PaulZC/Iridium_9603N_Solar_Beacon/img/Iridium_9603N_Solar_Beacon_4.JPG

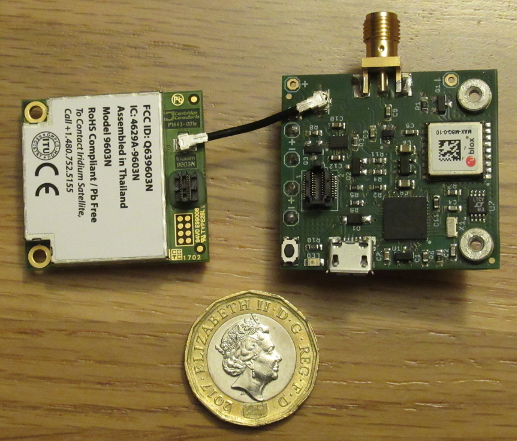
img/Iridium_9603N_Solar_Beacon_4.JPG
