PaulZC/Iridium_9603N_Solar_Beacon/Iridium_9603N_Solar_Beacon_Prototype.JPG

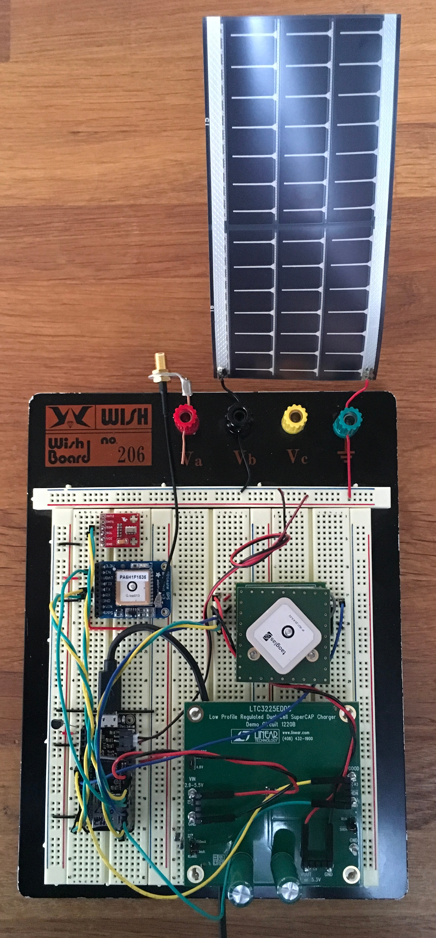
Iridium_9603N_Solar_Beacon_Prototype.JPG
