PaulZC/Iridium_9603N_Solar_Beacon/Iridium_9603N_Solar_Beacon_Prototype_Fritzing.png

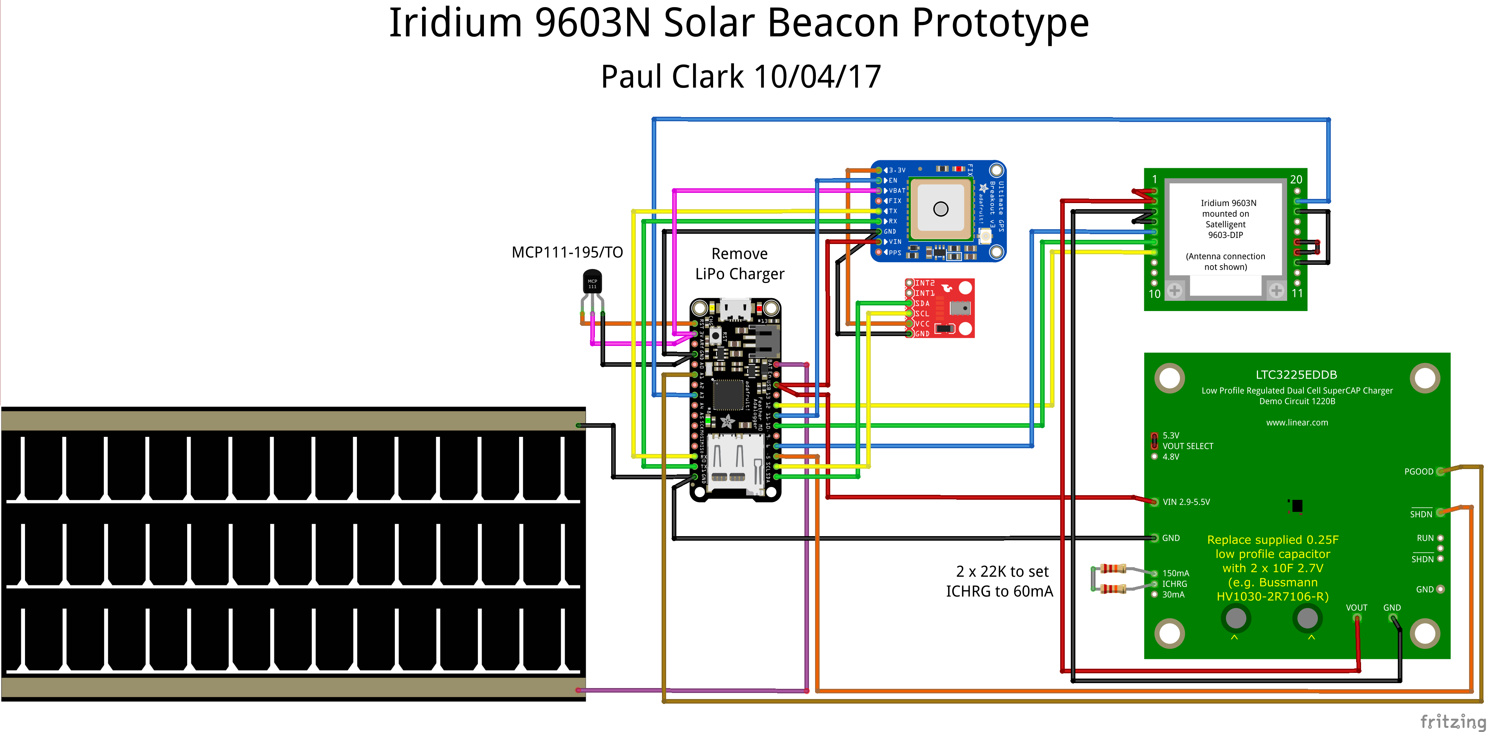
Iridium_9603N_Solar_Beacon_Prototype_Fritzing.png
